TilenTinta/Aquarium_Air_Pump_Controller/Images/PXL_20251029_190839017.jpg

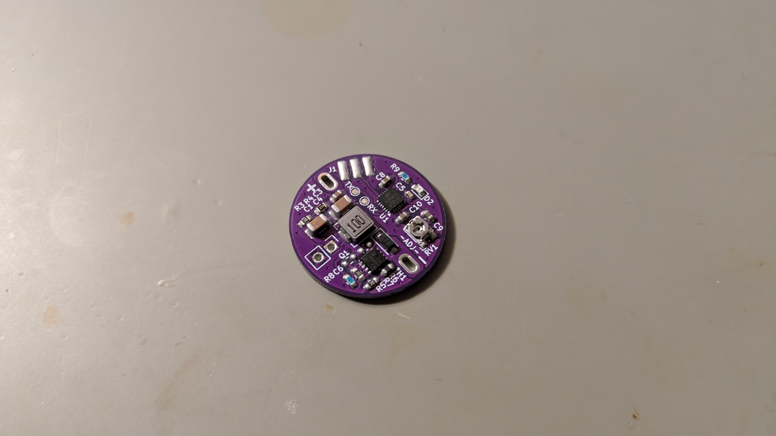
Images/PXL_20251029_190839017.jpg
